edirab/homemeteo-esp-01/imgs/orig/Image00001.jpg

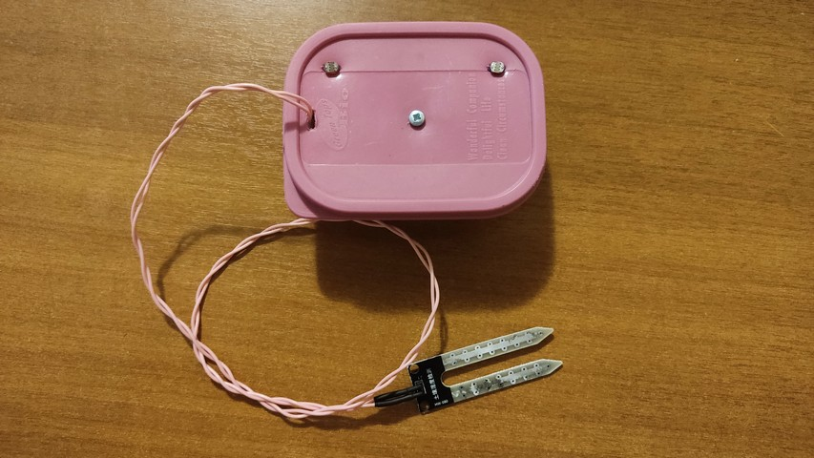
imgs/orig/Image00001.jpg
