edirab/homemeteo-esp-01/imgs/orig/Image00002.jpg

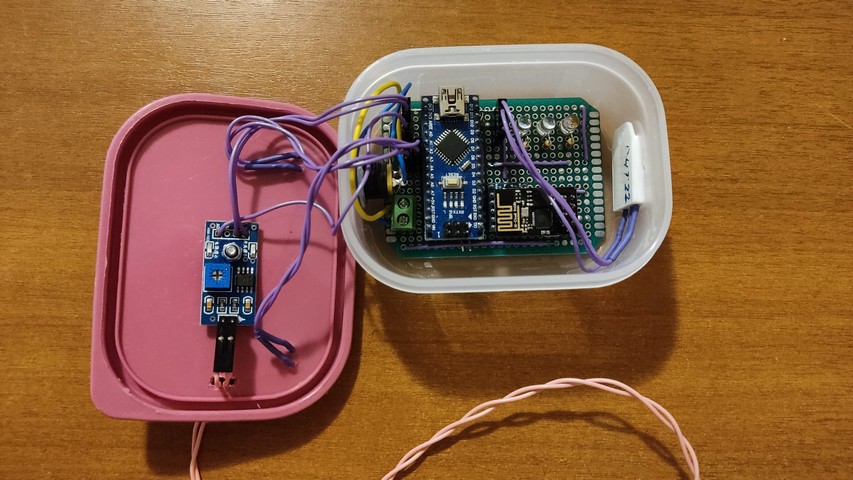
imgs/orig/Image00002.jpg
