edirab/homemeteo-esp-01/imgs/orig/Image00003.jpg

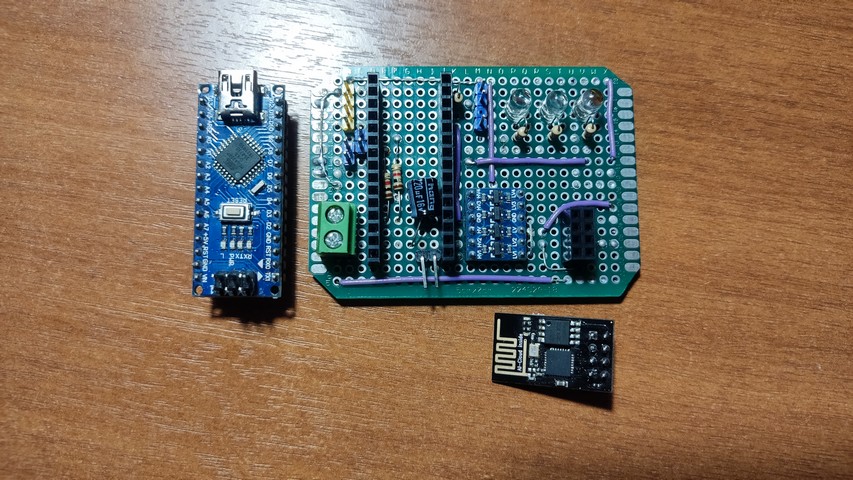
imgs/orig/Image00003.jpg
