edirab/homemeteo-esp-01/imgs/orig/Image00004.jpg

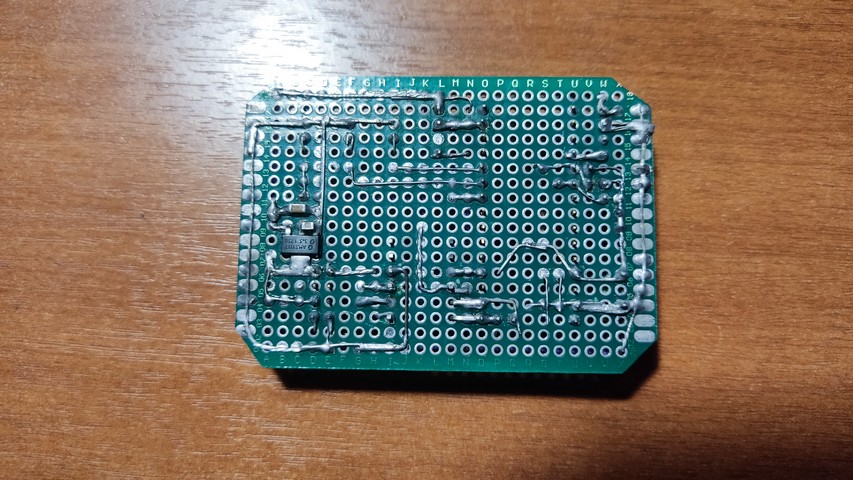
imgs/orig/Image00004.jpg
